opeRaptor/OTlite/Software/IMG_20170405_214132.jpg

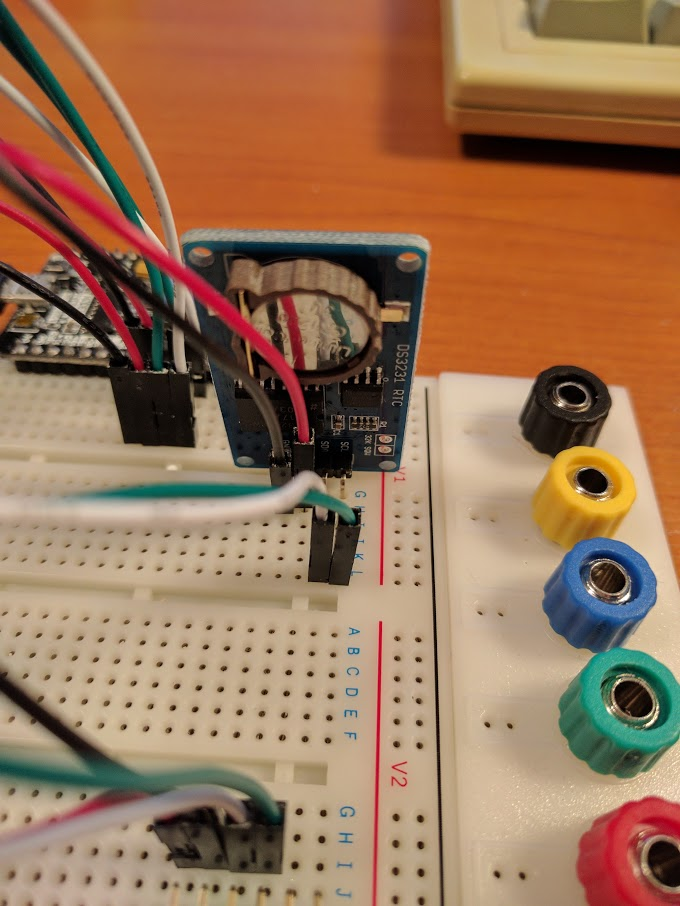
Software/IMG_20170405_214132.jpg
